kotiel/uvuk/uvuk-pic/uvuk-ap01-12.jpg

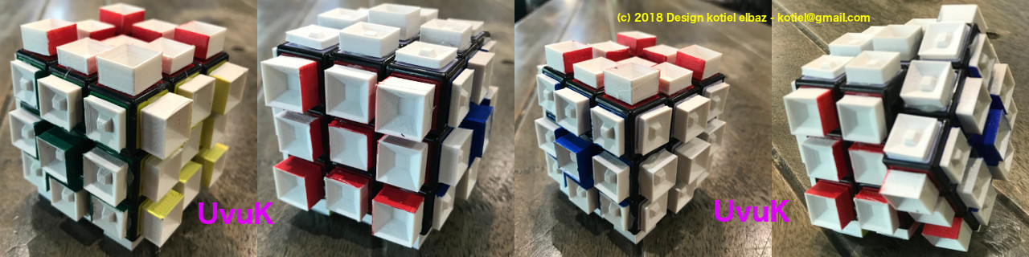
uvuk-pic/uvuk-ap01-12.jpg
