kotiel/uvuk/uvuk-pic/uvuk-ap01-13.jpg

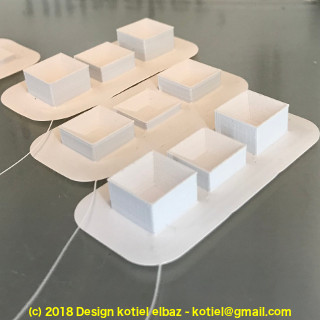
uvuk-pic/uvuk-ap01-13.jpg
