kotiel/uvuk/uvuk-pic/uvuk-ap01-15.jpg

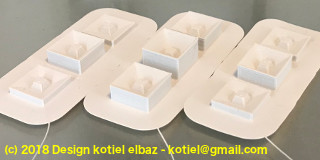
uvuk-pic/uvuk-ap01-15.jpg
