kotiel/uvuk/uvuk-pic/uvuk-ap04-01.jpg

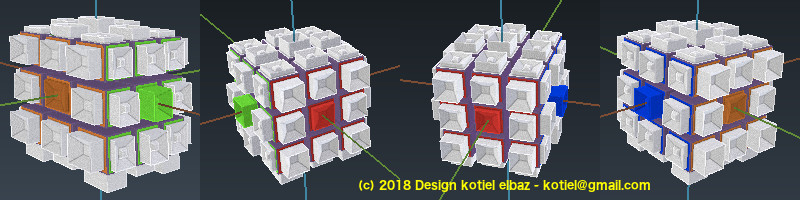
uvuk-pic/uvuk-ap04-01.jpg
