kotiel/uvuk/uvuk-pic/uvuk-ap04-03.jpg

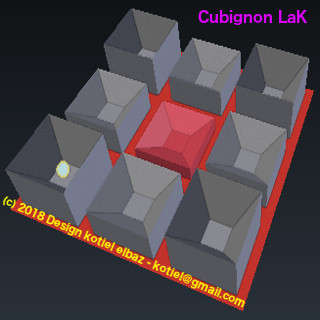
uvuk-pic/uvuk-ap04-03.jpg
