kotiel/uvuk/uvuk-pic/uvuk-ap04-04.jpg

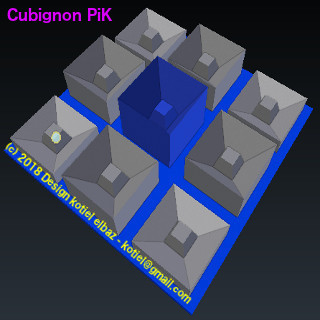
uvuk-pic/uvuk-ap04-04.jpg
