kotiel/uvuk/uvuk-pic/uvuk-ap04-05.jpg

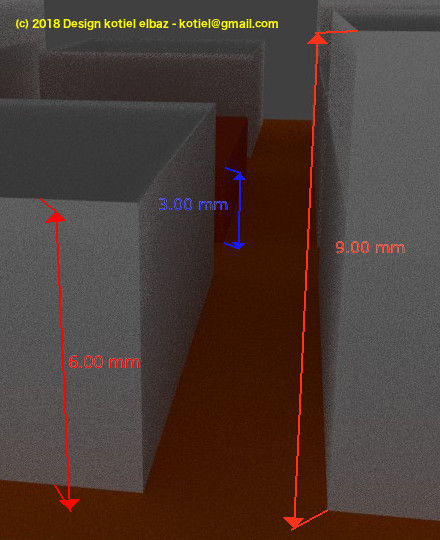
uvuk-pic/uvuk-ap04-05.jpg
