kotiel/uvuk/uvuk-pic/uvuk-ap09-f01d.jpg

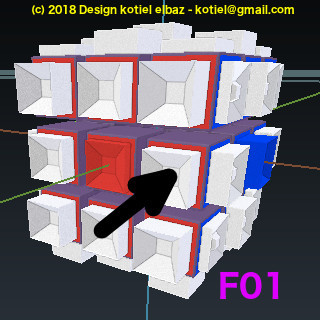
uvuk-pic/uvuk-ap09-f01d.jpg
