kotiel/uvuk/uvuk-pic/uvuk-ap09-f02g.jpg

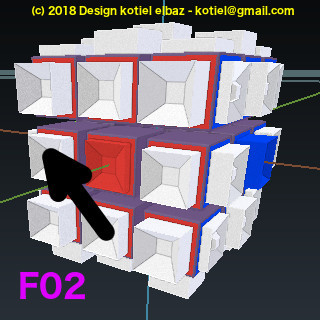
uvuk-pic/uvuk-ap09-f02g.jpg
